Siddhant779/FinalLab445L/sw/src/ILI9341.c

/*
 *
 *
 *              ILI9341 
 *
 *                       T_IRQ: --
 *                        T_DO: -
 *                       T_DIN: -
 *  SD_SCK: PB4           T_CS: -
 * SD_MISO: PB6          T_CLK: -
 * SD_MOSI: PB7           MISO: -
 *   SD_CS: PB0            LED: 3.3V
 *                         SCK: PA2
 *                        MOSI: PA5
 *                          DC: PA6
 *                       RESET: PA7
 *                          CS: PA3
 *                         GND: GND
 *                         VCC:  3.3V

 */
 



#include "ILI9341.h"
#include <stdio.h>
#include <stdint.h>
#include <stdlib.h>
#include "../inc/tm4c123gh6pm.h"





#define TFT_CS                  (*((volatile uint32_t *)0x40004020))
#define TFT_CS_LOW              0           // CS normally controlled by hardware
#define TFT_CS_HIGH             0x08
#define DC                      (*((volatile uint32_t *)0x40004100))
#define DC_COMMAND              0
#define DC_DATA                 0x40
#define RESET                   (*((volatile uint32_t *)0x40004200))
#define RESET_LOW               0
#define RESET_HIGH              0x20


#define MADCTL_MY 0x80  ///< Bottom to top
#define MADCTL_MX 0x40  ///< Right to left
#define MADCTL_MV 0x20  ///< Reverse Mode
#define MADCTL_ML 0x10  ///< LCD refresh Bottom to top
#define MADCTL_RGB 0x00 ///< Red-Green-Blue pixel order
#define MADCTL_BGR 0x08 ///< Blue-Green-Red pixel order
#define MADCTL_MH 0x04  ///< LCD refresh right to left


#define DELAY 0x80

void beginSPITransaction();
void endSPITransaction();

static uint8_t rotation;           // 0 to 3

static int16_t _width = ILI9341_TFTWIDTH;   // this could probably be a constant, except it is used in Adafruit_GFX and depends on image rotation
static int16_t _height = ILI9341_TFTHEIGHT;

uint32_t Xcord=53; // position along the horizonal axis 0 to 52
uint32_t Ycord=0; // position along the vertical axis 0 to 22
uint32_t bgColorChange = ILI9341_WHITE;

static const uint8_t Font[] = {
  0x00, 0x00, 0x00, 0x00, 0x00,
  0x3E, 0x5B, 0x4F, 0x5B, 0x3E,
  0x3E, 0x6B, 0x4F, 0x6B, 0x3E,
  0x1C, 0x3E, 0x7C, 0x3E, 0x1C,
  0x18, 0x3C, 0x7E, 0x3C, 0x18,
  0x1C, 0x57, 0x7D, 0x57, 0x1C,
  0x1C, 0x5E, 0x7F, 0x5E, 0x1C,
  0x00, 0x18, 0x3C, 0x18, 0x00,
  0xFF, 0xE7, 0xC3, 0xE7, 0xFF,
  0x00, 0x18, 0x24, 0x18, 0x00,
  0xFF, 0xE7, 0xDB, 0xE7, 0xFF,
  0x30, 0x48, 0x3A, 0x06, 0x0E,
  0x26, 0x29, 0x79, 0x29, 0x26,
  0x40, 0x7F, 0x05, 0x05, 0x07,
  0x40, 0x7F, 0x05, 0x25, 0x3F,
  0x5A, 0x3C, 0xE7, 0x3C, 0x5A,
  0x7F, 0x3E, 0x1C, 0x1C, 0x08,
  0x08, 0x1C, 0x1C, 0x3E, 0x7F,
  0x14, 0x22, 0x7F, 0x22, 0x14,
  0x5F, 0x5F, 0x00, 0x5F, 0x5F,
  0x06, 0x09, 0x7F, 0x01, 0x7F,
  0x00, 0x66, 0x89, 0x95, 0x6A,
  0x60, 0x60, 0x60, 0x60, 0x60,
  0x94, 0xA2, 0xFF, 0xA2, 0x94,
  0x08, 0x04, 0x7E, 0x04, 0x08,
  0x10, 0x20, 0x7E, 0x20, 0x10,
  0x08, 0x08, 0x2A, 0x1C, 0x08,
  0x08, 0x1C, 0x2A, 0x08, 0x08,
  0x1E, 0x10, 0x10, 0x10, 0x10,
  0x0C, 0x1E, 0x0C, 0x1E, 0x0C,
  0x30, 0x38, 0x3E, 0x38, 0x30,
  0x06, 0x0E, 0x3E, 0x0E, 0x06,
  0x00, 0x00, 0x00, 0x00, 0x00,
  0x00, 0x00, 0x5F, 0x00, 0x00,
  0x00, 0x07, 0x00, 0x07, 0x00,
  0x14, 0x7F, 0x14, 0x7F, 0x14,
  0x24, 0x2A, 0x7F, 0x2A, 0x12,
  0x23, 0x13, 0x08, 0x64, 0x62,
  0x36, 0x49, 0x56, 0x20, 0x50,
  0x00, 0x08, 0x07, 0x03, 0x00,
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
};

static const uint8_t cmd_ili9341[] = {
    25,

    ILI9341_SWRESET, DELAY, 150, // Software reset

    0xCB, 5, 0x39, 0x2C, 0x00, 0x34, 0x02,
    0xCF, 3, 0x00, 0xC1, 0x30,
    0xEF, 3, 0x03, 0x80, 0x02,
    0xE8, 3, 0x85, 0x00, 0x78,
    0xEA, 2, 0x00, 0x00,
    0xCF, 3, 0x00, 0XC1, 0X30,
    0xED, 4, 0x64, 0x03, 0x12, 0x81,
    0xF7, 1, 0x20,

    ILI9341_PWCTRL1, 1, 0x23, // Power control
    ILI9341_PWCTRL2, 1, 0x10, // Power control
    ILI9341_VMCTRL1, 2, 0x3E, 0x28, //0x3e, 0x28, // VCM control
    ILI9341_VMCTRL2, 1, 0x86, // VCM control2
    ILI9341_MADCTL, 1, 0x48, // Memory Access Control
    ILI9341_PIXFMT, 1, 0x55, //16-bit    0x66 24-bit
    ILI9341_INVOFF, 0,
    ILI9341_FRMCTR1, 2, 0x00, 0x10, // FrameRate Control 119Hz
    ILI9341_DISCTRL, 4, 0x08, 0x82, 0x27, 0x00, // Display Function Control
    0x30, 4, 0x00, 0x00, 0x01, 0x3F,
    0xF2, 1, 0x00,
    ILI9341_GAMMASET, 1, 0x01, // Gamma curve selected
    ILI9341_GMCTRP1, 15, 0x0F, 0x31, 0x2B, 0x0C, 0x0E, 0x08,
        0x4E, 0xF1, 0x37, 0x07, 0x10, 0x03, 0x0E, 0x09, 0x00, // Set Gamma
    ILI9341_GMCTRN1, 15, 0x00, 0x0E, 0x14, 0x03, 0x11, 0x07,
        0x31, 0xC1, 0x48, 0x08, 0x0F, 0x0C, 0x31, 0x36, 0x0F, // Set Gamma
    ILI9341_SLPOUT, DELAY, 200,  // Normal display on, 10ms delay
    ILI9341_DISPON, DELAY, 100
};

void Delay1ms(uint32_t n){uint32_t volatile time;
  while(n){
    time = 72724*2/91;  // 1msec, tuned at 80 MHz
    while(time){
      time--;
    }
    n--;
  }
}

static void writeCommand(uint8_t c) {
                                        // wait until SSI0 not busy/transmit FIFO empty
  while((SSI0_SR_R&SSI_SR_BSY)==SSI_SR_BSY){};
  TFT_CS = TFT_CS_LOW;
  DC = DC_COMMAND;
  SSI0_DR_R = c;                        // data out
                                        // wait until SSI0 not busy/transmit FIFO empty
  while((SSI0_SR_R&SSI_SR_BSY)==SSI_SR_BSY){};
}

static void writeData(uint8_t d) {
  while((SSI0_SR_R&SSI_SR_TNF)==0){};   // wait until transmit FIFO not full
  DC = DC_DATA;
  SSI0_DR_R = d;                        // data out
}


void static ILI9341_setColor(uint32_t rgb) {
    /* // 18-bit, 6-6-6
    uint8_t r = (rgb & 0x3F0000) >> 16;
    uint8_t g = (rgb & 0x003F00) >> 8;
    uint8_t b = (rgb & 0x00003F);

    writeData(b << 2);
    writeData(g << 2);
    writeData(r << 2);

    */

      // 16-bit, 5-6-5
    //    uint8_t r = (rgb & 0xF80000) >> 19;
    //    uint8_t g = (rgb & 0x00FC00) >> 10;
    //    uint8_t b = (rgb & 0x0000F8) >> 3;
    //NEED TO CHANGE THIS CODE 
    uint8_t r = (rgb & 0xF80000) >> 19;
    uint8_t g = (rgb & 0x00FC00) >> 10;
    uint8_t b = (rgb & 0x0000F8) >> 3;

    writeData((r << 3) | (g >> 3));
    writeData((g << 5) | (b));
}

void static ILI9341_setCoords(uint16_t x0, uint16_t y0, uint16_t x1, uint16_t y1) {
    writeCommand(ILI9341_CASET); // Column addr set
    writeData(y0>>8);
    writeData(y0);     // YSTART
    writeData(y1>>8);
    writeData(y1);     // YEND

    writeCommand(ILI9341_PASET); // Row addr set
    writeData(x0>>8);
    writeData(x0);     // XSTART
    writeData(x1>>8);
    writeData(x1);     // XEND

    writeCommand(ILI9341_RAMWR);    // write to RAM
}

static void deselect(void) {
    // wait until SSI0 not busy/transmit FIFO empty
  while((SSI0_SR_R&SSI_SR_BSY)==SSI_SR_BSY){};
  TFT_CS = TFT_CS_HIGH;
}



//------------------------------------------------------------------
void ILI9341_init() {
    //GPIOPinTypeGPIOOutput(GPIO_PORTE_BASE, GPIO_PIN_5);

    SYSCTL_RCGCSSI_R |= 0x01;  // activate SSI0
    SYSCTL_RCGCGPIO_R |= 0x01; // activate port A
    while((SYSCTL_PRGPIO_R&0x01)==0){}; // allow time for clock to start

    // toggle RST low to reset; CS low so it'll listen to us
    // SSI0Fss is temporarily used as GPIO
    GPIO_PORTA_DIR_R |= 0xC8;             // make PA3,6,7 out
    GPIO_PORTA_AFSEL_R &= ~0xC8;          // disable alt funct on PA3,6,7
    GPIO_PORTA_DEN_R |= 0xC8;             // enable digital I/O on PA3,6,7
                                        // configure PA3,6,7 as GPIO
    GPIO_PORTA_PCTL_R = (GPIO_PORTA_PCTL_R&0x00FF0FFF)+0x00000000;
    GPIO_PORTA_AMSEL_R &= ~0xC8;          // disable analog functionality on PA3,6,7
    //GPIOPinWrite(GPIO_PORTE_BASE, GPIO_PIN_5, GPIO_PIN_5);
    //sleep(10);
    //GPIOPinWrite(GPIO_PORTE_BASE, GPIO_PIN_5, 0);
    //sleep(20);
    //GPIOPinWrite(GPIO_PORTE_BASE, GPIO_PIN_5, GPIO_PIN_5);
    //sleep(150);
    TFT_CS = TFT_CS_LOW;
    //RESET = RESET_HIGH;
    GPIO_PORTA_DATA_R |= 0x80; 
    Delay1ms(500);
    //RESET = RESET_LOW;
    GPIO_PORTA_DATA_R &= ~0x80; 
    Delay1ms(500);
    RESET = RESET_HIGH;
    GPIO_PORTA_DATA_R |= 0x80; 
    Delay1ms(500);

    // initialize SSI0
    GPIO_PORTA_AFSEL_R |= 0x2C;           // enable alt funct on PA2,3,5
    GPIO_PORTA_DEN_R |= 0x2C;             // enable digital I/O on PA2,3,5
                                        // configure PA2,3,5 as SSI
    GPIO_PORTA_PCTL_R = (GPIO_PORTA_PCTL_R&0xFF0F00FF)+0x00202200;
    GPIO_PORTA_AMSEL_R &= ~0x2C;          // disable analog functionality on PA2,3,5
    SSI0_CR1_R &= ~SSI_CR1_SSE;           // disable SSI
    SSI0_CR1_R &= ~SSI_CR1_MS;            // master mode
                                        // configure for system clock/PLL baud clock source
    SSI0_CC_R = (SSI0_CC_R&~SSI_CC_CS_M)+SSI_CC_CS_SYSPLL;

                                        // SysClk/(CPSDVSR*(1+SCR))
                                        // 80/(10*(1+0)) = 8 MHz (slower than 4 MHz)
    //SSI0_CPSR_R = (SSI0_CPSR_R&~SSI_CPSR_CPSDVSR_M)+16;
    //SSI0_CPSR_R = (SSI0_CPSR_R&~SSI_CPSR_CPSDVSR_M)+10;

    SSI0_CPSR_R = (SSI0_CPSR_R&~SSI_CPSR_CPSDVSR_M)+4; // must be even number
//    SSI0_CPSR_R = (SSI0_CPSR_R&~SSI_CPSR_CPSDVSR_M)+6; // must be even number
    SSI0_CR0_R &= ~(SSI_CR0_SCR_M |       // SCR = 0 (8 Mbps data rate)
                  SSI_CR0_SPH |         // SPH = 0
                  SSI_CR0_SPO);         // SPO = 0
                                        // FRF = Freescale format
    SSI0_CR0_R = (SSI0_CR0_R&~SSI_CR0_FRF_M)+SSI_CR0_FRF_MOTO;
                                        // DSS = 8-bit data
    SSI0_CR0_R = (SSI0_CR0_R&~SSI_CR0_DSS_M)+SSI_CR0_DSS_8;
    SSI0_CR1_R |= SSI_CR1_SSE;            // enable SSI

    commandList(cmd_ili9341);

    ILI9341_fillScreen(0);                 // set screen to black
}

// Companion code to the above tables.  Reads and issues
// a series of LCD commands stored in ROM byte array.
void commandList(const uint8_t *addr) {

  uint8_t numCommands, numArgs;
  uint16_t ms;

  numCommands = *(addr++);               // Number of commands to follow
  while(numCommands--) {                 // For each command...
    writeCommand(*(addr++));             //   Read, issue command
    numArgs  = *(addr++);                //   Number of args to follow
    ms       = numArgs & DELAY;          //   If hibit set, delay follows args
    numArgs &= ~DELAY;                   //   Mask out delay bit
    while(numArgs--) {                   //   For each argument...
      writeData(*(addr++));              //     Read, issue argument
    }

    if(ms) {
      ms = *(addr++);             // Read post-command delay time (ms)
      if(ms == 255) ms = 500;     // If 255, delay for 500 ms
      Delay1ms(ms);
    }
  }
}

//  Bottom-left corner is (0, 0). Up = +y, Right = +x
void ILI9341_drawPixel(uint32_t x, uint32_t y, uint32_t rgb) {
    if((x > _width) || (y > _height)) return;

    beginSPITransaction();

    ILI9341_setCoords(x,y,x,y);

    ILI9341_setColor(rgb);

    deselect();
    endSPITransaction();
}

void ILI9341_drawHLineOtherWay(uint32_t x, uint32_t y, uint32_t l, uint32_t rgb, uint8_t width) {
    if((x > _width) || (y > _height)) return;
    //if(x - l > 0) l = x-0;

  for(int s = 0; s < width; s++) {
    beginSPITransaction();

    ILI9341_setCoords(x,y+s,x-l,y+s);

    for(uint32_t i = 0; i < l; i++) {
        ILI9341_setColor(rgb);
    }
    deselect();
    endSPITransaction();
  }
}

//  Coordinate is left-most pixel of line
void ILI9341_drawHLine(uint32_t x, uint32_t y, uint32_t l, uint32_t rgb, uint8_t width) {
    if((x > _width) || (y > _height)) return;
    if(x + l > _width) l = _width-x;

  for(int s = 0; s < width; s++) {
    beginSPITransaction();

    ILI9341_setCoords(x,y+s,x+l,y+s);

    for(uint32_t i = 0; i < l; i++) {
        ILI9341_setColor(rgb);
    }
    deselect();
    endSPITransaction();
  }
}

//  Coordinate is bottom pixel of line
void ILI9341_drawVLine(uint32_t x, uint32_t y, uint32_t l, uint32_t rgb, uint8_t width) {
    if((x > _width) || (y > _height)) return;
    if(y + l > _width) l = _height-y;


    for(int s = 0; s < width; s ++){
      beginSPITransaction();

      ILI9341_setCoords(x+s,y,x+s,y+l);

      for(uint16_t i = 0; i < l; i++) {
          ILI9341_setColor(rgb);
      }
      deselect();
      endSPITransaction();
    }
}

void ILI9341_drawColors(uint32_t x, uint32_t y, int32_t *rgbArr, uint16_t totalPixels) {
    if((x > _width) || (y > _height)) return;

    if(x + totalPixels > _width) totalPixels = _width-x;

    beginSPITransaction();

    ILI9341_setCoords(x,y,x+totalPixels,y);

    for(uint32_t i = 0; i < totalPixels; i++) {
        ILI9341_setColor(rgbArr[i]);
    }

    deselect();
}

//  Coordinate is left-most pixel of line
void ILI9341_drawHLineMulticolored(uint32_t x, uint32_t y, uint32_t *rgb, uint32_t *num, uint32_t n) {
    if((x > _width) || (y > _height)) return;

    uint32_t l = 0;
    for(int i = 0; i < n; i++) {
        l += num[i];
    }

    if(x + l >= _width) l = _width-x-1;

    beginSPITransaction();

    ILI9341_setCoords(x,y,x+l,y);

    uint32_t j;
    uint32_t loops;
    for(int i = n-1; i >= 0; i--) {
        loops = num[i];
        for(j = 0; j < loops && l-- > 0; j++) {
            ILI9341_setColor(rgb[i]);
        }
    }
    deselect();
}

//  coordinate is bottom-left of rectangle
void ILI9341_fillRect(uint32_t x, uint32_t y, uint32_t w, uint32_t h, uint32_t rgb) {
    if((x > _width) || (y > _height)) return;

    if(x + w >= _width) w = _width - x;
    if(y + h >= _height) h = _height - y;

    beginSPITransaction();

    ILI9341_setCoords(x, y, x+w, y+h);

    for(y = h; y > 0; y--) {
        for(x = w; x > 0; x--) {
            ILI9341_setColor(rgb);
        }
    }
    deselect();
}

void ILI9341_fillScreen(uint32_t rgb) {
    ILI9341_fillRect(0, 0, _width, _height, rgb);
}

void beginSPITransaction(void) {
    SYSCTL_RCGCSSI_R |= 0x01;  // activate SSI0
}

void endSPITransaction(void) {
    while((SSI0_SR_R&SSI_SR_BSY)==SSI_SR_BSY){};
    SYSCTL_RCGCSSI_R &= ~0x01;  // deactivate SSI0
}

//------------ST7735_DrawBitmap------------
// Displays a 16-bit color BMP image.  A bitmap file that is created
// by a PC image processing program has a header and may be padded
// with dummy columns so the data have four byte alignment.  This
// function assumes that all of that has been stripped out, and the
// array image[] has one 16-bit halfword for each pixel to be
// displayed on the screen (encoded in reverse order, which is
// standard for bitmap files).  An array can be created in this
// format from a 24-bit-per-pixel .bmp file using the associated
// converter program.
// (x,y) is the screen location of the lower left corner of BMP image
// Requires (11 + 2*w*h) bytes of transmission (assuming image fully on screen)
// Input: x     horizontal position of the bottom left corner of the image, columns from the left edge
//        y     vertical position of the bottom left corner of the image, rows from the top edge
//        image pointer to a 16-bit color BMP image
//        w     number of pixels wide
//        h     number of pixels tall
// Output: none
// Must be less than or equal to 128 pixels wide by 160 pixels high
//FOR ILI THE X IS THE RIGHT SIDE AND THE Y IS THE BOTTOM PART OF IT 
void ILI9341_DrawBitmap(uint16_t x, uint16_t y, const uint16_t *image, uint16_t w, uint16_t h){
  int16_t skipC = 0;                      // non-zero if columns need to be skipped due to clipping
  int16_t originalWidth = w;              // save this value; even if not all columns fit on the screen, the image is still this width in ROM
  int i = w*(h - 1);

  if((x >= _width) || ((y - h + 1) >= _height) || ((x + w) <= 0) || (y < 0)){
    return;                             // image is totally off the screen, do nothing
  }
  if((w > _width) || (h > _height)){    // image is too wide for the screen, do nothing
    //***This isn't necessarily a fatal error, but it makes the
    //following logic much more complicated, since you can have
    //an image that exceeds multiple boundaries and needs to be
    //clipped on more than one side.
    return;
  }
  if((x + w - 1) >= _width){            // image exceeds right of screen
    skipC = (x + w) - _width;           // skip cut off columns
    w = _width - x;
  }
  if((y - h + 1) < 0){                  // image exceeds top of screen
    i = i - (h - y - 1)*originalWidth;  // skip the last cut off rows
    h = y + 1;
  }
  if(x < 0){                            // image exceeds left of screen
    w = w + x;
    skipC = -1*x;                       // skip cut off columns
    i = i - x;                          // skip the first cut off columns
    x = 0;
  }
  if(y >= _height){                     // image exceeds bottom of screen
    h = h - (y - _height + 1);
    y = _height - 1;
  }

  ILI9341_setCoords(x, y-h+1, x+w-1, y);

  for(y=0; y<h; y=y+1){
    for(x=0; x<w; x=x+1){
                                        // send the top 8 bits
      writeData((uint8_t)(image[i] >> 8));
                                        // send the bottom 8 bits
      writeData((uint8_t)image[i]);
      i = i + 1;                        // go to the next pixel
    }
    i = i + skipC;
    i = i - 2*originalWidth;
  }

  deselect();
}


void ILI9341_DrawCharS(uint16_t x, uint16_t y, char c, uint32_t textColor, uint32_t bgColor, uint8_t size){
  uint8_t line; // vertical column of pixels of character in font
  int32_t i, j;
  if((x >= _width)            || // Clip right
     (y >= _height)           || // Clip bottom
     ((x + 6 * size - 1) < 0) || // Clip left
     ((y + 8 * size - 1) < 0))   // Clip top
    return;

  for (i=0; i<6; i++ ) {
    if (i == 5)
      line = 0x0;
    else
      line = Font[(c*5)+i];
    for (j = 0; j<8; j++) {
      if (line & 0x1) {
        if (size == 1) // default size
          ILI9341_drawPixel(x-i, y+j, textColor);
          //ILI9341_drawPixel(y-j, x-i, textColor);
          //ST7735_DrawPixel(x+i, y+j, textColor);
        else {  // big size
          //ILI9341_fillRect(y-(j*size), x-(i*size), size, size, textColor);
          ILI9341_fillRect(x-(i*size), y+(j*size), size, size, textColor);
          //ST7735_FillRect(x+(i*size), y+(j*size), size, size, textColor);
        }
      } else if (bgColorChange != textColor) {
        if (size == 1) // default size
          //ILI9341_drawPixel(y-j, x-i, bgColor);
          ILI9341_drawPixel(x-i, y+j, bgColorChange);
          //ST7735_DrawPixel(x+i, y+j, bgColor);
        else {  // big size
          //ILI9341_fillRect(y-j*size, x-i*size, size, size, bgColor);
          ILI9341_fillRect(x-(i*size), y+(j*size), size, size, bgColorChange);
          //ST7735_FillRect(x+i*size, y+j*size, size, size, bgColor);
        }
      }
      line >>= 1;
    }
  }
}

uint32_t ILI9341_DrawString(uint16_t x, uint16_t y, char *pt, uint32_t textColor, uint8_t size){
  uint32_t count = 0;
  if(y>24) return 0;
  while(*pt){
    ILI9341_DrawCharS(x*6, y*10, *pt, textColor, ILI9341_BLACK, size);
    pt++;
    x = x-size;
    if(x < 0) return count;  // number of characters printed
    count++;
  }
  return count;  // number of characters printed
}

uint32_t ILI9341_DrawStringCord(uint16_t x, uint16_t y, char *pt, uint32_t textColor, uint8_t size){
  uint32_t count = 0;
  if(y>240) return 0;
  while(*pt){
    ILI9341_DrawCharS(x, y, *pt, textColor, ILI9341_BLACK, size);
    pt++;
    x = x-(size*6);
    if(x < 0) return count;  // number of characters printed
    count++;
  }
  return count;  // number of characters printed
}


void ILI9341_OutChar(char ch, uint8_t size, uint32_t textColor){
  if((ch == 10) || (ch == 13) || (ch == 27)){
    Ycord+=size; Xcord=52;
    if(Ycord>24){
      Ycord = 0;
    }
    ILI9341_DrawString(0,Ycord,"                     ",textColor, size);
    return;
  }
  ILI9341_DrawCharS(Xcord*6,Ycord*10,ch,textColor,bgColorChange, size);
  Xcord-=size;
  if(Xcord < 0){
    Xcord = 0;
    ILI9341_DrawCharS(Xcord*6,Ycord*10,'*',textColor,bgColorChange, size);
  }
  return;
}

void ILI9341_OutString(char *ptr, uint32_t textColor){
  while(*ptr){
    ILI9341_OutChar(*ptr, 1, textColor);
    ptr = ptr + 1;
  }
}

void ILI9341_setBGColor(uint32_t bgColor) {
  bgColorChange = bgColor;
}

void ILI9341_OutStringSize(char *ptr, uint32_t textColor, uint8_t size){
  while(*ptr){
    ILI9341_OutChar(*ptr, size, textColor);
    ptr = ptr + 1;
  }
}

void ILI9341_SetCursor(uint32_t newX, uint32_t newY){
  if((newX > 53) || (newY > 24)){       // bad input
    return;                             // do nothing
  }
  Xcord = newX;
  Ycord = newY;
}

void setRotation(uint8_t m) {
  writeCommand(ILI9341_MADCTL);
  rotation = m % 4; // can't be higher than 3
  //
  switch (rotation) {
  case 0:
    m = (MADCTL_MX | MADCTL_BGR);
    _width = ILI9341_TFTWIDTH;
    _height = ILI9341_TFTHEIGHT;
    writeData(MADCTL_MX | MADCTL_BGR);
    Delay1ms(100);
    break;
  case 1:
    m = (MADCTL_MV | MADCTL_BGR);
    _width = ILI9341_TFTHEIGHT;
    _height = ILI9341_TFTWIDTH;
    writeData(MADCTL_MV | MADCTL_BGR);
    Delay1ms(100);
    break;
  case 2:
    m = (MADCTL_MY | MADCTL_BGR);
    _width = ILI9341_TFTWIDTH;
    _height = ILI9341_TFTHEIGHT;
    writeData(MADCTL_MY | MADCTL_BGR);
    Delay1ms(100);
    break;
  case 3:
    m = (MADCTL_MX | MADCTL_MY | MADCTL_MV | MADCTL_BGR);
    _width = ILI9341_TFTHEIGHT;
    _height = ILI9341_TFTWIDTH;
    writeData(MADCTL_MX | MADCTL_MY | MADCTL_MV | MADCTL_BGR);
    Delay1ms(100);
    break;
  }
}
