Siddhant779/FinalLab445L/sw/src/Switch.h

// Switch.h

/*
// Siddhant Pandit 
// Wyatt Cole 
// This part of the module will be used for 
*/

#include <stdint.h>
#include <stdbool.h>
#include "./inc/tm4c123gh6pm.h"

// Initializes PC4,5,6,7 and PF4 as edge-triggered switches
void switch_init(void);

uint8_t get_input(void);
